9bitsdelta/Audio-Mixer/rezumat/media/PCB_back.png

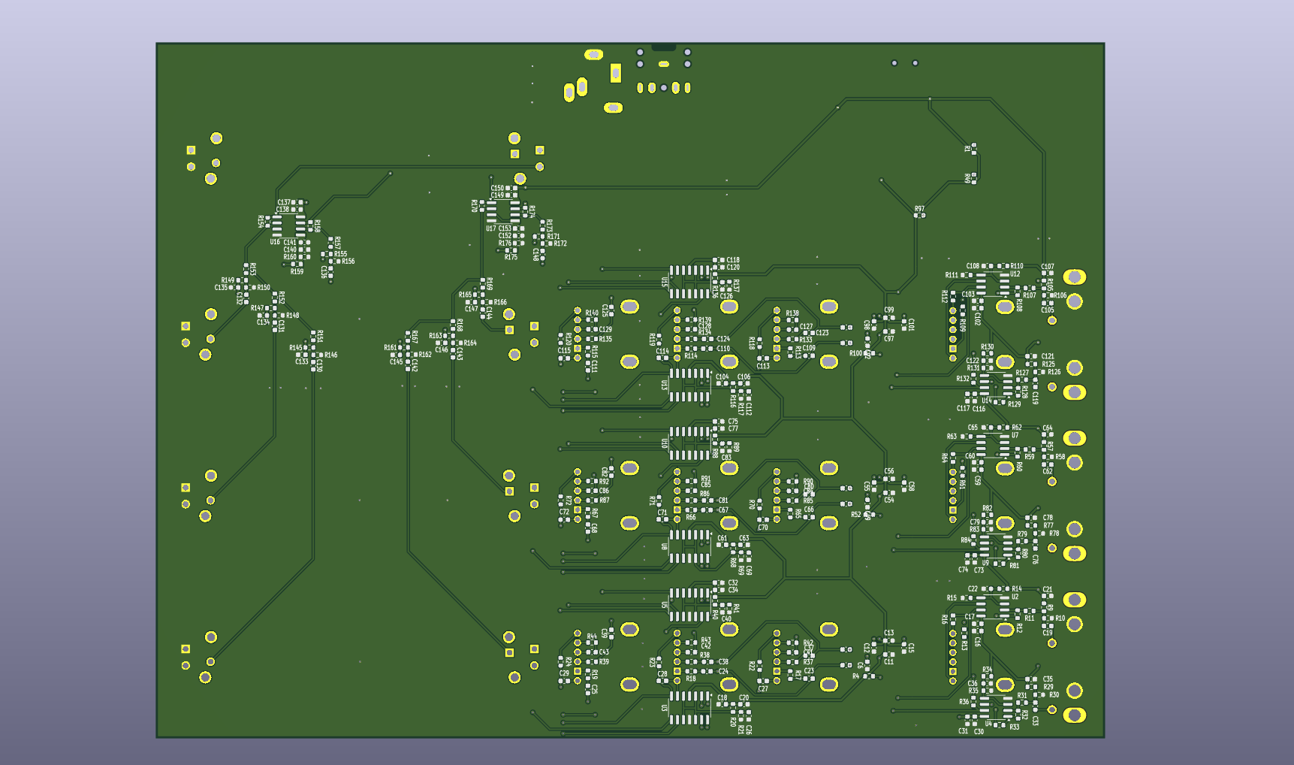
rezumat/media/PCB_back.png
