9bitsdelta/Audio-Mixer/rezumat/media/sim_eq-ac-high.png

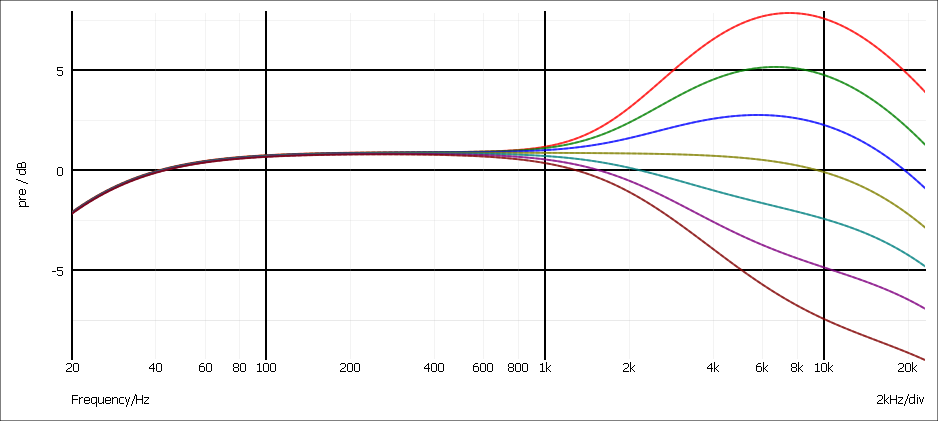
rezumat/media/sim_eq-ac-high.png
