9bitsdelta/Audio-Mixer/rezumat/media/sim_eq-ac-low.png

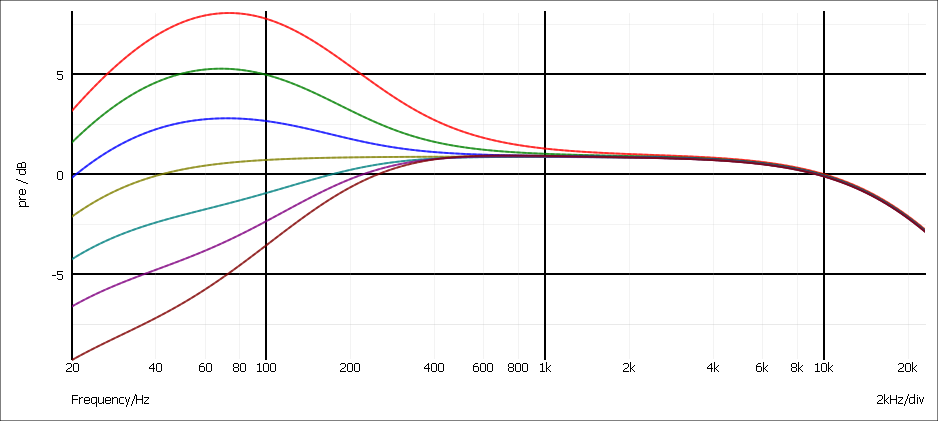
rezumat/media/sim_eq-ac-low.png
