9bitsdelta/Audio-Mixer/rezumat/media/sim_eq-ac-mid.png

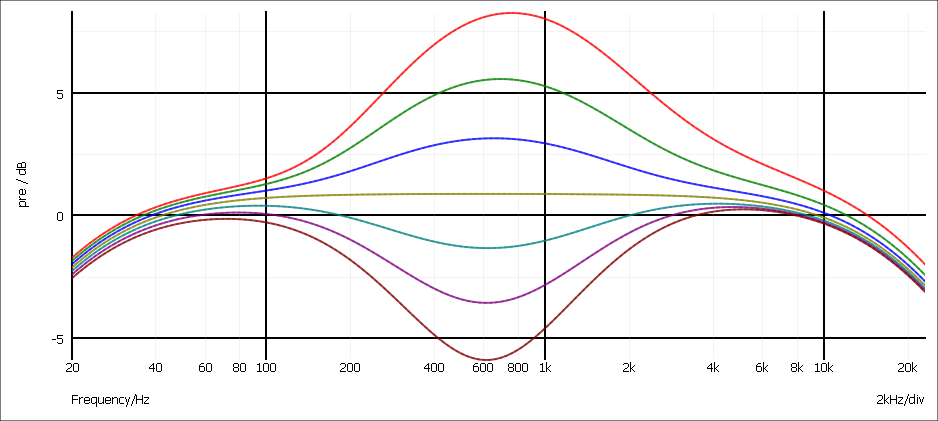
rezumat/media/sim_eq-ac-mid.png
