9bitsdelta/Audio-Mixer/rezumat/media/sim_preamp-out.png

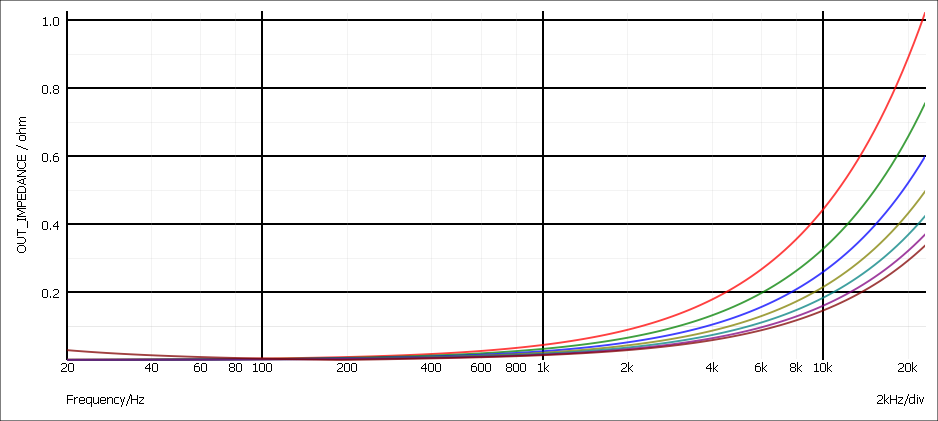
rezumat/media/sim_preamp-out.png
