9bitsdelta/Audio-Mixer/rezumat/svg-inkscape/opamps-amp_svg-raw.png

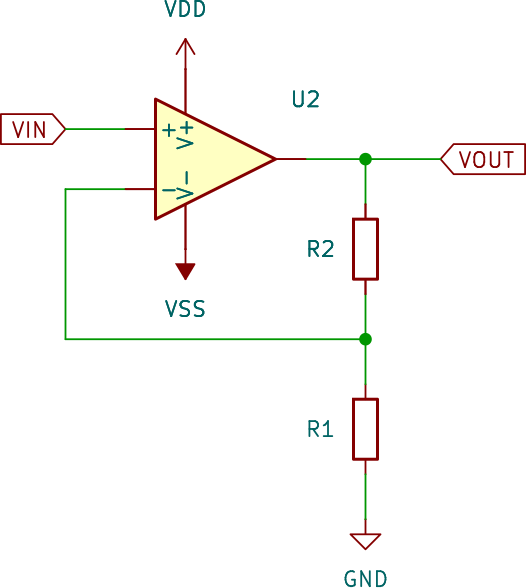
rezumat/svg-inkscape/opamps-amp_svg-raw.png
