9bitsdelta/Audio-Mixer/rezumat/svg-inkscape/opamps-highshelf_svg-raw.png

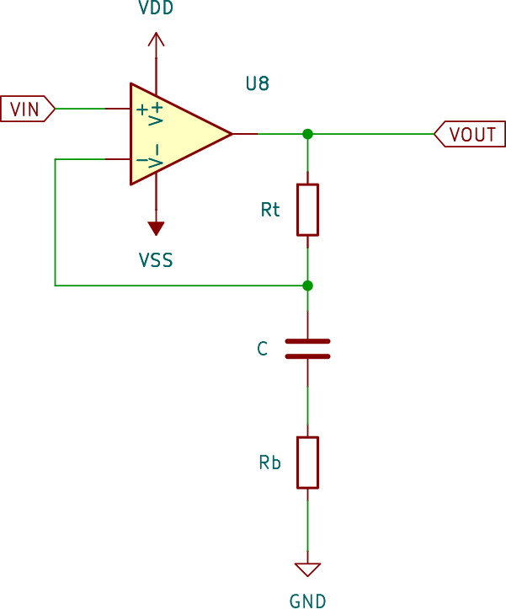
rezumat/svg-inkscape/opamps-highshelf_svg-raw.png
