9bitsdelta/Audio-Mixer/rezumat/svg-inkscape/opamps-invfilt_svg-raw.png

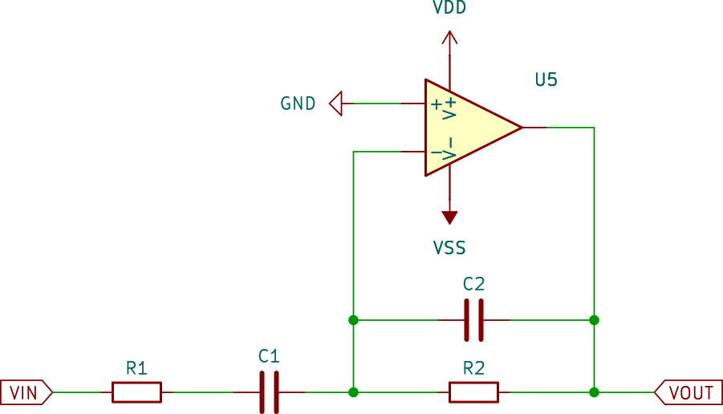
rezumat/svg-inkscape/opamps-invfilt_svg-raw.png
