9bitsdelta/Audio-Mixer/rezumat/svg-inkscape/opamps-lowshelf_svg-raw.png

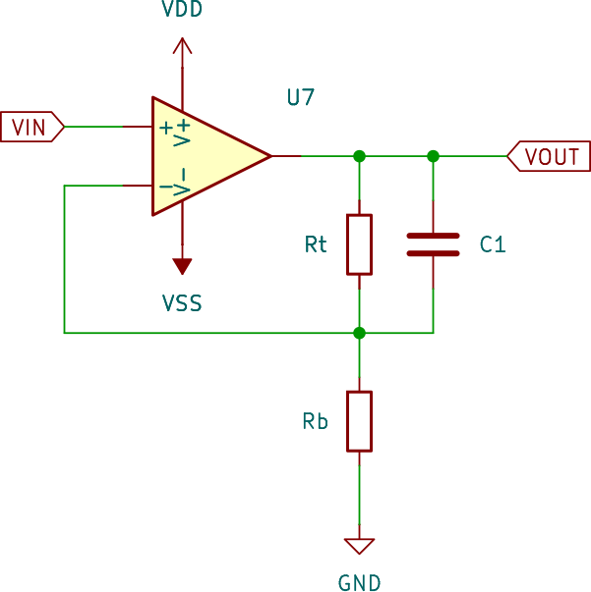
rezumat/svg-inkscape/opamps-lowshelf_svg-raw.png
