9bitsdelta/Audio-Mixer/rezumat/svg-inkscape/opamps-sumamp_svg-raw.png

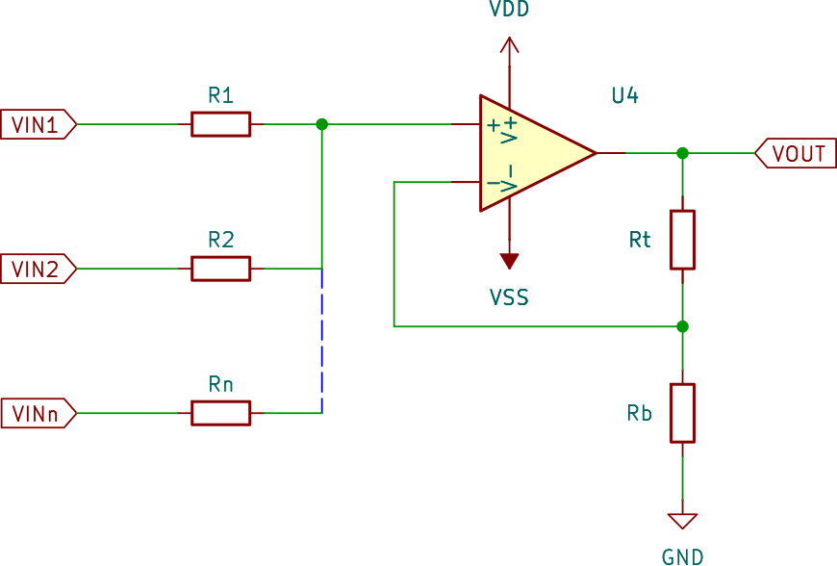
rezumat/svg-inkscape/opamps-sumamp_svg-raw.png
